AliDismail/FrameLock/version 2/code/raspberry_code (work in progress)/dataset/Ali Ismail/Ali Ismail_20251102_230833.jpg

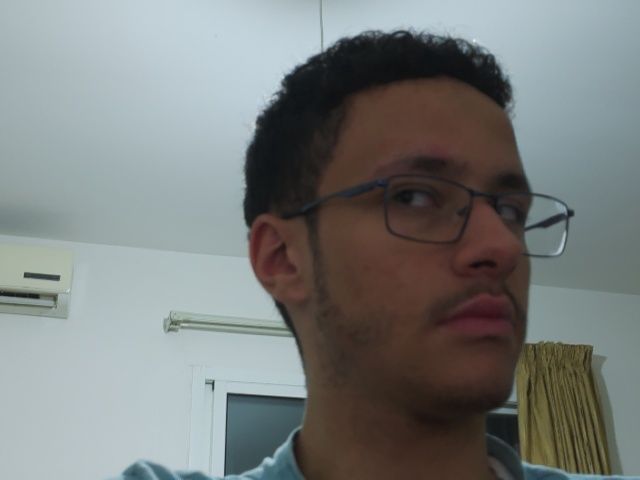
version 2/code/raspberry_code (work in progress)/dataset/Ali Ismail/Ali Ismail_20251102_230833.jpg
