AliDismail/FrameLock/version 2/code/raspberry_code (work in progress)/dataset/Nour Zebian/Nour Zebian_20251113_211007.jpg

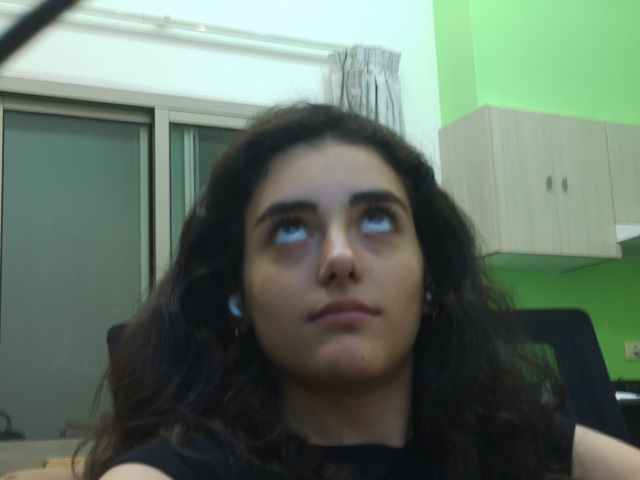
version 2/code/raspberry_code (work in progress)/dataset/Nour Zebian/Nour Zebian_20251113_211007.jpg
